TD-er/NodeMCU_PCB/board_rev2/Etchable/PDF/CO2 meter rev2_etch_silk_bottom_mirror.pdf

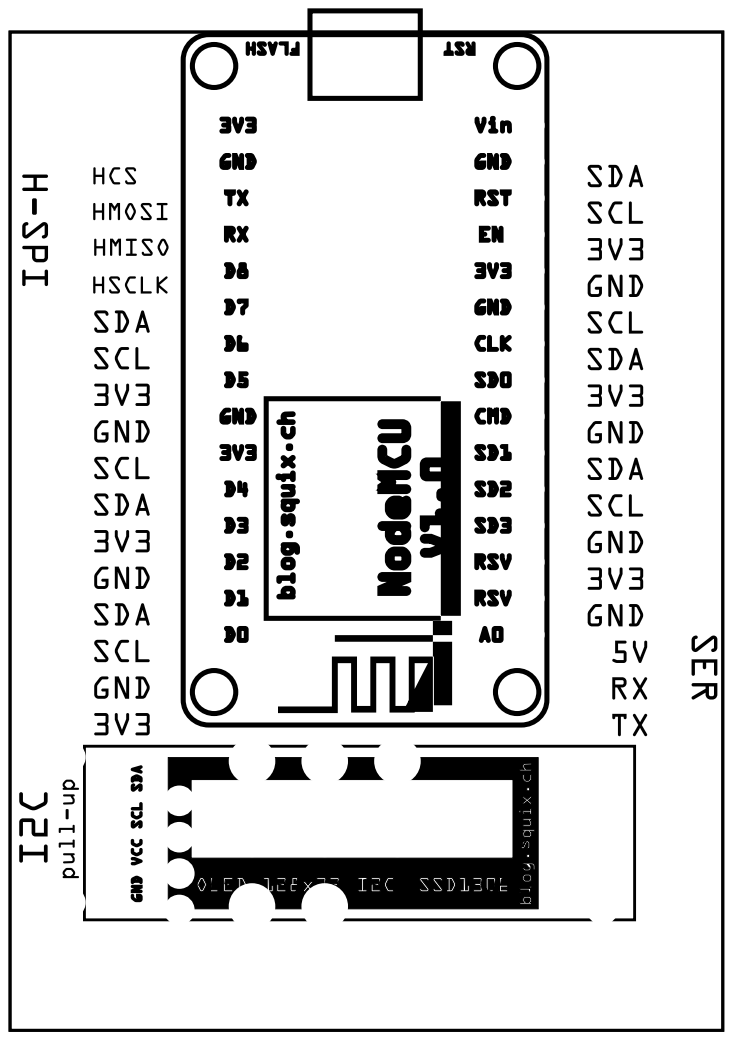
[picture p15: page 1]
