TD-er/NodeMCU_PCB/board_rev2/Etchable/PDF/CO2 meter rev2_etch_silk_top.pdf

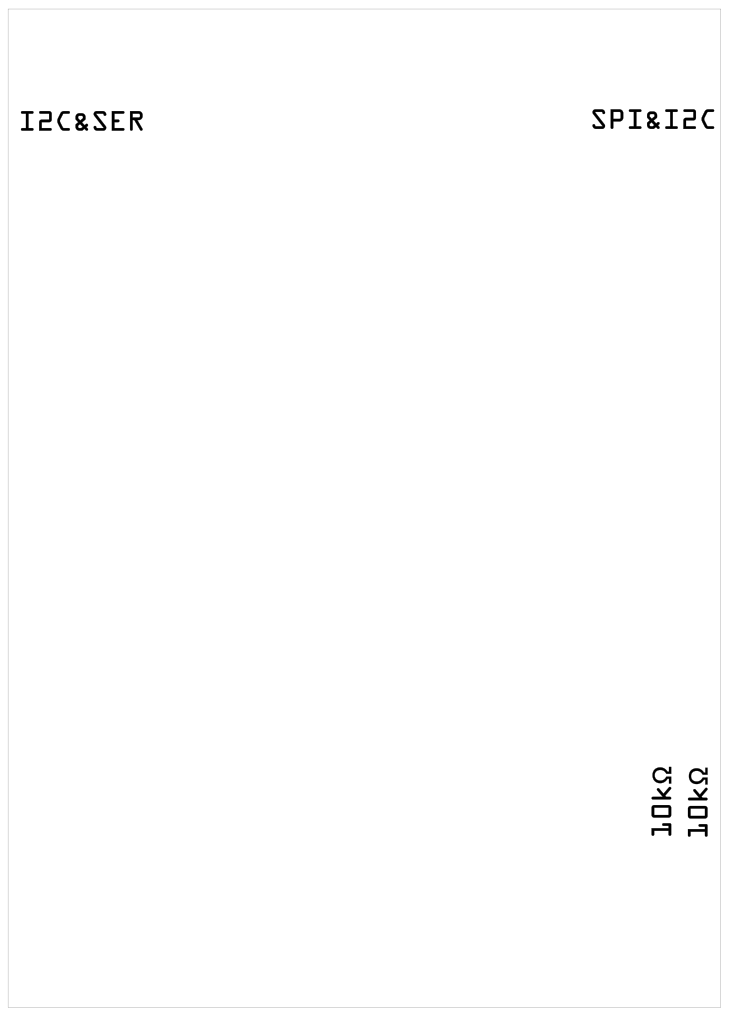
[picture p16: page 1]
