TD-er/NodeMCU_PCB/board_rev2/Etchable/PDF/CO2 meter rev2_etch_silk_top_mirror.pdf

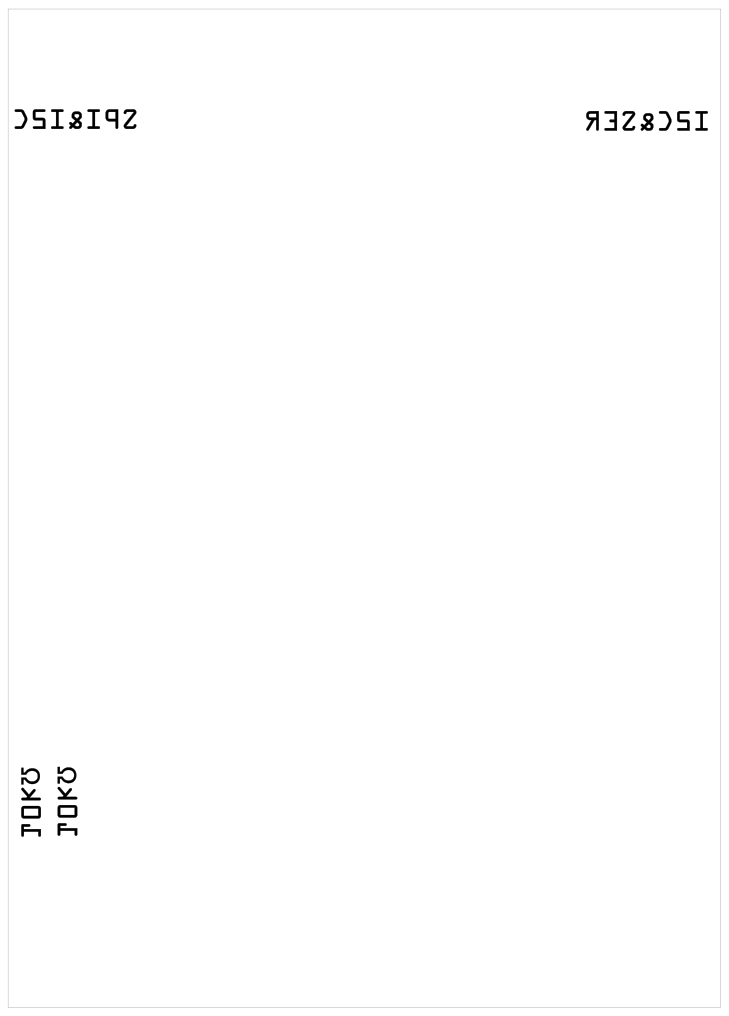
[picture p17: page 1]
